ejovrh/misko/misko-prototype/functions.h

// forward declaration of this shitty function (it's at the very end of this file)
void poor_mans_debugging(void);

/* auto_timeout() - returns 1 if enough time has passed
 *  returns:
 *    1 if time is up
 *    0 otherwise
 *
 * input arguments:
 *    uint32_t some_button_press_time - time of button press
 *    uint8_t timeout - timeout in seconds
 *
 * times are in seconds !!
 */
uint8_t inline auto_timeout(const uint32_t in_button_press_time, const uint8_t timeout_val)
{
  return (abs( in_button_press_time - millis()) / 1000 > timeout_val ?  1 :  0);
}

// reads a byte from the ADXL345
byte adxl345_readByte(const byte registerAddress) // reads one byte at registerAddress
{
		digitalWrite(SPI_SS_ADXL345_pin, LOW); // reserve the slave
   	SPI.transfer(0x80 | registerAddress); // set the MSB to 1 (the read command), then send address to read from
		byte retval = SPI.transfer(0x00); // send one byte (0x00) into the circular FIFO buffer, get one byte back
		digitalWrite(SPI_SS_ADXL345_pin, HIGH); // release the slave
    return retval;  // return value
}

// writes a byte into the ADXL345
bool adxl345_writeByte(const byte registerAddress, const byte value)
{
	digitalWrite(SPI_SS_ADXL345_pin, LOW); // signal the slave
	SPI.transfer(registerAddress); // send address to write to
	SPI.transfer(value); // send the byte
	digitalWrite(SPI_SS_ADXL345_pin, HIGH); // release the slave

	if (adxl345_readByte(registerAddress) != value) // verify correct setting
	{
		Serial.print(F("registerAddress was not set:"));Serial.print(registerAddress);Serial.print("-");Serial.println(value);
		return 1;
	}

	return 0;
}

// writes one byte data into the FeRAM at address addr
uint8_t FeRAMWriteByte(const uint16_t addr, const byte data)
{
	if (addr > 0x7FFF) // if we try to go past the max. RAM address
		return 1;	// return something

	uint8_t addr_msb = (addr >> 8) & 0xFF;
	uint8_t addr_lsb = addr & 0xFF;

	// put the FeRAM module into RW mode
	digitalWrite(SPI_FRAM_SS_pin, LOW); // select the FeRAM module
	SPI.transfer(CMD_WREN);	// issue WREN command
	digitalWrite(SPI_FRAM_SS_pin, HIGH); // de-select the FeRAM module

	// put into write mode, send address, then write data
	digitalWrite(SPI_FRAM_SS_pin, LOW); // select the FeRAM module
	SPI.transfer(CMD_WRITE);	// issue WRITE command
	SPI.transfer(addr_msb); // send address most significant byte
	SPI.transfer(addr_lsb); // send address least significant byte

	SPI.transfer(data); // write data into module

	digitalWrite(SPI_FRAM_SS_pin, HIGH); // de-select the FeRAM module

	return 0;
}

// returns one one byte from the FeRAM at addr
byte FeRAMReadByte(const uint16_t addr)
{
	byte retval;
	if (addr > 0x7FFF) // if we try to go past the max. RAM address
		return -1;	// return something

	uint8_t addr_msb = (addr >> 8) & 0xFF;
	uint8_t addr_lsb = addr & 0xFF;

	digitalWrite(SPI_FRAM_SS_pin, LOW); // select the FeRAM module
	SPI.transfer(CMD_READ); // send READ command
	SPI.transfer(addr_msb);	// send address most significant byte
	SPI.transfer(addr_lsb); // send address least significant byte

	retval = SPI.transfer(0xFF); // send on byte of crap into the circular buffer, get one byte back

	digitalWrite(SPI_FRAM_SS_pin, HIGH); // de-select the FeRAM module

	return retval; // returns read out data
}

// writes string data of len lenght into FeRAM at address addr
uint8_t FeRAMWriteStr(const uint16_t addr, const char *data, uint8_t len)
{
	if (addr > 0x7FFF) // if we try to go past the max. RAM address
		return 1;	// return something

	uint8_t addr_msb = (addr >> 8) & 0xFF;
	uint8_t addr_lsb = addr & 0xFF;

	// put the FeRAM module into RW mode
	digitalWrite(SPI_FRAM_SS_pin, LOW); // select the FeRAM module
	SPI.transfer(CMD_WREN);	// issue WREN command
	digitalWrite(SPI_FRAM_SS_pin, HIGH); // de-select the FeRAM module

	// put into write mode, send address, then write data
	digitalWrite(SPI_FRAM_SS_pin, LOW); // select the FeRAM module
	SPI.transfer(CMD_WRITE);	// issue WRITE command
	SPI.transfer(addr_msb); // send address most significant byte
	SPI.transfer(addr_lsb); // send address least significant byte

	for (uint8_t i = 0; i< len; i++)
		SPI.transfer( *(data+i) ); // write data into module

	digitalWrite(SPI_FRAM_SS_pin, HIGH); // de-select the FeRAM module

	return 0;
}

// reads a string in FeRAM at addess addr of lenght len into buff
uint8_t FeRAMReadString(const uint16_t addr, char *out_data, uint8_t len)
{
	if (addr > 0x7FFF) // if we try to go past the max. RAM address
		return -1;	// return something

	memset(out_data, '\0', len);

	uint8_t addr_msb = (addr >> 8) & 0xFF;
	uint8_t addr_lsb = addr & 0xFF;

	digitalWrite(SPI_FRAM_SS_pin, LOW); // select the FeRAM module
	SPI.transfer(CMD_READ); // send READ command
	SPI.transfer(addr_msb);	// send address most significant byte
	SPI.transfer(addr_lsb); // send address least significant byte

	for(uint8_t i = 0; i < len; i++)
	{
		*(out_data+i) = SPI.transfer(0xFF); // send on byte of crap into the circular buffer, get one byte back
	}

	digitalWrite(SPI_FRAM_SS_pin, HIGH); // de-select the FeRAM module
}

 // returns the external voltage reference in volts
inline float read_Varef() // the external reference voltage is set to 2.50V via a zener diode
{
	return AREF_VOLTAGE;
}

// returns the voltage on a given pin
float calculate_voltage(int pin) // calculates the voltage on a given pin by considering read_aref_V()
{
	uint16_t reading = analogRead(pin); // read raw sensor data (voltage) - 10bit resolution -> values form 0-1023
	return (float) (reading * read_Varef() / 1024.0); // converting reading to voltage, based on AREF;
}

// calculates the temperature by reading voltage from the TMP36
inline float calculate_temperature(void) // executed from loop()
{
	return (calculate_voltage(TMP36_Vsense_pin) - 0.5) * 100.0 ;  // 10 mv per C, 500 mV offset
}

// callback for Vcc
const char *fn_cb_get_Vcc(m2_rom_void_p element)
{
	static char retval[9]; // will return something like Vcc3.23V
	static char tmp_vcc[5]; // holds e.g "3.23" as an intermediate conversion to string

	dtostrf(val_Vcc, 3, 2, tmp_vcc); // convert the float into a string
	sprintf(retval, "Vcc%sV", tmp_vcc ); // print the string into the retval string
	return retval;
}

// callback for battery percentage
const char *fn_cb_get_bat_pct(m2_rom_void_p element)
{
	// FIXME

	const char retval[9];
	sprintf("batA %3d%", val_batA_pct);
	return retval;

	//return "foo";
	//dtostrf(val_batA_pct, 3, 0, bat_a_pct + 4*sizeof(char)); // instead, this works
		//// http://www.atmel.com/webdoc/AVRLibcReferenceManual/group__avr__stdlib_1ga060c998e77fb5fc0d3168b3ce8771d42.html
	//strcat(bat_a_pct, "% ");
	//return bat_a_pct;
}

// handler for the bluetooth power toggle button
void handle_bluetooth_button(void)
{
	/* purpose: control BT power based on feram settings

		the button functions are, if auto mode is enabled:
			- press and the device turns on. after EERPOM_BLUETOOTH_AUTO_TIMEOUT_INDEX is over, turn off
			- hold pressed to keep the device on until manually turned off by again holding pressed (timeout then doesnt count)

		if auto mode is not enabled, the button does nothing.

		in order to accomplish this, we need to track in what mode we are in (EERPOM_BLUETOOTH_POWER_INDEX),
			how long the device is supposed to be turned on (EERPOM_BLUETOOTH_AUTO_TIMEOUT_INDEX) and how long the BT button
			was held pressed (bluetooth_button_press_time and bluetooth_button_release_time).

		additionally, we need to make sure that one button press equals one event - we need to know if the button is
			held pressed or not (flag_bluetooth_power_toggle_pressed)

	*/

	if (!flag_bluetooth_power_toggle_pressed) // if the button is not flagged as pressed
	{
		if(digitalRead(menu_gprs_power_button_pin) == HIGH) // if the button gets pressed
		{
			flag_bluetooth_power_toggle_pressed = 1; // flag the button as pressed, prevents multiple calls

	if ( ( (FeRAMReadByte(FERAM_DEVICE_MISC_CFG2) >> FERAM_DEVICE_MISC_CFG2_BLUETOOTH_POWER) & 0x03 ) != 2 )
				return; // do nothing

			if (flag_bluetooth_power_keep_on) // prevent the timer from starting when we want to turn off manually toggled power
				return; // do nothing

			bluetooth_button_press_time = millis(); // record time of button press; this is used in a bit down to keep bt on on auto
			digitalWrite(Bluetooth_wakeup_pin, LOW); // turn on the device
			flag_bluetooth_is_on = 1; // set flag to on
		}
	}
	else // the button is already flagged as pressed == is held pressed
	{
	if ( ( (FeRAMReadByte(FERAM_DEVICE_MISC_CFG2) >> FERAM_DEVICE_MISC_CFG2_BLUETOOTH_POWER) & 0x03 ) != 2 )
			return;

		if ( digitalRead(menu_gprs_power_button_pin) == LOW) // the button is released
		{
			bluetooth_button_release_time = millis(); // record time of button release
			flag_bluetooth_power_toggle_pressed = 0; // mark button as released

			if (abs(bluetooth_button_release_time - bluetooth_button_press_time) > 500) // if button is held long enough
						flag_bluetooth_power_keep_on = !flag_bluetooth_power_keep_on; // toggle the power state on -> off and vice versa
		}
	}

	if ( ( (FeRAMReadByte(FERAM_DEVICE_MISC_CFG2) >> FERAM_DEVICE_MISC_CFG2_BLUETOOTH_POWER) & 0x03 ) != 2 )
		return; // do nothing

	if (flag_bluetooth_power_keep_on) // if the BT device is marked to be kept on
		return;	// do nothing

	if ( flag_bluetooth_is_on && auto_timeout(bluetooth_button_press_time, FeRAMReadByte(FERAM_BLUETOOTH_AUTO_TIMEOUT)) ) // if the device is on and enough time has passed
	{
			digitalWrite(Bluetooth_wakeup_pin, HIGH); // turn off the device
			flag_bluetooth_is_on = 0; // set flag to off
			// flag_bluetooth_power_keep_on = 0;
	}
}

// handler for the bluetooth power toggle button
void handle_gprs_button(void)
{
	/*	purpose: control the GPRS module based on FeRAM settings
	 *
	 *	this function is called from loop and checks if a button press occured
	 *		if it did, it acts upon it
	 *
	 *	prerequisites for any GPRS action:
	 *		1. power on the GSM module & dialup
	 *		2. authenticate on HTTP server
	 *		3. do the task at hand
	 *		4. report status
	 *		5. tear down the connection & power off the GSM module
	 */

	if (!flag_gprs_push_pressed) // if the button is not flagged as pressed
	{
		if(digitalRead(menu_gprs_power_button_pin) == HIGH) // if the button gets pressed
		{
			uint8_t config = ( ( FeRAMReadByte(FERAM_DEVICE_MISC_CFG2) >> FERAM_DEVICE_MISC_CFG2_GPRS_FUNCTION) & 0x03 ); // fish out the device setting in FeRAM
			flag_gprs_push_pressed = 1; // flag the button as pressed, prevents multiple calls

			if (!config) // if it is set to do nothing...
				return; // then do nothing

			if (config == 1) // immediate push of position
			{
				Serial.println("immediate push of position");
			}

			if (config == 2) // upload all of today's logs
			{
				Serial.println("upload of today's logs");
			}

			if (config == 3) // FIXME: GPS fucking
			{
				poor_mans_debugging();
			}
		}
	}
	else // the button is already flagged as pressed
	{
		if ( digitalRead(menu_gprs_power_button_pin) == LOW) // the button is released
			flag_gprs_push_pressed = 0; // mark button as released
	}
}

// puts the oled to sleep accrding to config setting
void handle_lcd_sleep(void)
{
	if (flag_oled_sleep || ( (FeRAMReadByte(FERAM_DEVICE_MISC_CFG1) >> FERAM_DEVICE_MISC_CFG1_OLED_AUTO_POWER) & 0x01 ) ) // dont do anything on "on" setting or in sleep mode
		return;

	if (auto_timeout(lcd_button_press_time, FeRAMReadByte(FERAM_OLED_AUTO_TIMEOUT) )) // true if time is up
	{
		flag_oled_sleep = 1;
		OLED.sleepOn();
	}
}

// calculates NMEA checksum
uint8_t getCheckSum(char *string)
{
  int XOR = 0;

  // for (int i = 1; i < 20; i++)
  for (uint8_t i = 1; i < strlen(string) -1; i++)
    XOR = XOR ^ *(string+i);

  return XOR;
}

// NMEA checksum calculator
int16_t parseHex(char g)
{
  if (g >= '0' && g <= '9')
    return (g - '0');
  else
    if (g >= 'A' && g <= 'F')
      return (g + 10 - 'A');
    else
      if (g >= 'a' && g <= 'f')
        return (g + 10 - 'a');

  return (-1);
}

// sets the RMC/GGA sentence frequency by sending the EM406A module an appropriate NMEA config sentence
void gps_adjust_log_freq(void) // operates directly off values stored in FeRAM
{
	/* valid for MTK3333 and similar chipsets
	*	314_PMTK_API_SET_NMEA_OUTPUT is what configures it
	*	fields:
	*			0 NMEA_SEN_GLL, GPGLL interval - Geographic Position - Latitude longitude
	*->		1 NMEA_SEN_RMC, GNRMC interval - Recommended Minimum Specific GNSS Sentence
	*			2 NMEA_SEN_VTG, GPVTG interval - Course Over Ground and Ground Speed
	*->		3 NMEA_SEN_GGA, GPGGA interval - GPS Fix Data
	*->		4 NMEA_SEN_GSA, GPGSA interval - GNSS DOPS and Active Satellites
	*->		5 NMEA_SEN_GSV, GPGSV interval - GNSS Satellites in View
	*			6 NMEA_SEN_GRS, GPGRS interval - GNSS Range Residuals
	*			7 NMEA_SEN_GST, GPGST interval - GNSS Pseudorange Errors Statistics
	*
	*			13 NMEA_SEN_MALM, PMTKALM interval - GPS almanac information
	*			14 NMEA_SEN_MEPH, PMTKEPH interval - GPS ephmeris information
	*			15 NMEA_SEN_MDGP, PMTKDGP interval - GPS differential correction information
	*			16 NMEA_SEN_MDBG, PMTKDBG interval  MTK debug information
	*			17 NMEA_SEN_ZDA, GPZDA interval - Time & Date
	*			18 NMEA_SEN_MCHN, PMTKCHN interval - GNSS channel status
	*			19 NMEA_SEN_DTM, GPDTM interval - Datum reference
	*
	*		NMEA checksum calculator:
	*			http://www.hhhh.org/wiml/proj/nmeaxor.html
	*
	*/

	sprintf(gps_command_buffer, "$PMTK314,0,%d,0,%d,%d,%d,0,0,0,0,0,0,0,0,0,0,0,0,0,0*", // construct the command string
		(uint8_t) ( (FeRAMReadByte(FERAM_GPS_GPRMC_GGA_GSA_FREQ) >> FERAM_GPS_GPRMC_GGA_FREQ) & 0x0F ), // RMC - index 1
		(uint8_t) ( (FeRAMReadByte(FERAM_GPS_GPRMC_GGA_GSA_FREQ) >> FERAM_GPS_GPRMC_GGA_FREQ) & 0x0F ), // GGA - index 3
		(uint8_t) ( (FeRAMReadByte(FERAM_GPS_GPRMC_GGA_GSA_FREQ) >> FERAM_GPS_GPGSA_FREQ) & 0x0F ), // GGA - index 4
		(uint8_t) ( (FeRAMReadByte(FERAM_GPS_GPZDA_GSV_FREQ) >> FERAM_GPS_GPGSV_FREQ) & 0x0F )); // GSV - field 5

	sprintf(gps_command_buffer + strlen(gps_command_buffer), "%02X", getCheckSum(gps_command_buffer)); // append the checksum
	Serial.println(gps_command_buffer);
	gps.println(gps_command_buffer);
	return;
}

// callback for data datetime_ok button
void fn_cb_button_datetime_ok(m2_el_fnarg_p fnarg)
{
	m2_SetRootExtended(&top_el_expandable_menu, 1, 0);
}

// callback for data position_ok button
void fn_cb_button_position_ok(m2_el_fnarg_p fnarg)
{
	m2_SetRootExtended(&top_el_expandable_menu, 2, 0);
}

// callback for data cellular_ok button
void fn_cb_button_cellular_ok(m2_el_fnarg_p fnarg)
{
	m2_SetRootExtended(&top_el_expandable_menu, 3, 0);
}

// callback for data-device_status_ok button
void fn_cb_button_device_status_ok(m2_el_fnarg_p fnarg)
{
	m2_SetRootExtended(&top_el_expandable_menu, 4, 0);
}

// callback for settings logging_ok button
void fn_cb_button_logging_ok(m2_el_fnarg_p fnarg)
{
	m2_SetRootExtended(&top_el_expandable_menu, 2, 0);
}

// callback for settings serial_ok button
void fn_cb_button_serial_ok(m2_el_fnarg_p fnarg)
{
	m2_SetRootExtended(&top_el_expandable_menu, 3, 0);
}

// callback for settings timezone_ok button
void fn_cb_button_timezone_ok(m2_el_fnarg_p fnarg)
{
	m2_SetRootExtended(&top_el_expandable_menu, 4, 0);
}

// callback for settings bluetooth_ok button
void fn_cb_button_bluetooth_ok(m2_el_fnarg_p fnarg)
{
	m2_SetRootExtended(&top_el_expandable_menu, 5, 0);
}

// callback for settings display_ok button
void fn_cb_button_display_ok(m2_el_fnarg_p fnarg)
{
	m2_SetRootExtended(&top_el_expandable_menu, 6, 0);
}

// callback for settings gps_ok button
void fn_cb_button_gps_ok(m2_el_fnarg_p fnarg)
{
	m2_SetRootExtended(&top_el_expandable_menu, 7, 0);
}

// callback for settings gsm_ok button
void fn_cb_button_gsm_ok(m2_el_fnarg_p fnarg)
{
	m2_SetRootExtended(&top_el_expandable_menu, 8, 0);
}

// callback for settings accelerometer_ok button
void fn_cb_button_accelerometer_ok(m2_el_fnarg_p fnarg)
{
	m2_SetRootExtended(&top_el_expandable_menu, 9, 0);
}

// callback for UTC display
const char *fn_cb_get_utc(m2_rom_void_p element)
{
	static char retval[4] = ""; // e.g. -12 or  +3
	int8_t tz = (int8_t) FeRAMReadByte(FERAM_DEVICE_TIMEZONE); // fetch the setting from FeRAM

	if (tz < 0 )
		itoa(tz, retval, 10); // will have the "-" automatically
	else
	{
		retval[0] = '+';	// manually set the "+" sign
		retval[1] = '\0'; // terminate
		itoa(tz, retval+sizeof(char), 10);
	}
	return retval;
}

// callback for GSM device power status
const char *fn_cb_get_gsm_power_status(m2_rom_void_p element)
{
	if (flag_gsm_on)
		return "on";

	return "off";
;}

// callback for GSM device network status
const char *fn_cb_get_gsm_network_status(m2_rom_void_p element)
{
	if (!flag_gsm_on) // if the device is off
		return "n/a";

	return "netw";
}

// callback for GSM device upload status
// TODO - implement it
const char *fn_cb_get_gsm_upload_status(m2_rom_void_p element)
{
	if (!flag_gsm_on) // if the device is off
	return "n/a";

	return "foo1";
}

// callback for GSM device power status
const char *fn_cb_get_gsm_foo1(m2_rom_void_p element)
{
	if (!flag_gsm_on) // if the device is off
		return "n/a";

	return "foo1";
}

// callback for GSM device power status
const char *fn_cb_get_gsm_foo2(m2_rom_void_p element)
{
	if (!flag_gsm_on) // if the device is off
		return "n/a";

	return "foo2";
}

// callback for GSM device power status
const char *fn_cb_get_gsm_foo3(m2_rom_void_p element)
{
	if (!flag_gsm_on) // if the device is off
		return "n/a";

	return "foo3";
}

// callback for temperature
const char *fn_cb_get_temperature(m2_rom_void_p element)
{
	static char retval[6]; // holds retval of e.g. "T+24C" of "T-10C"
	sprintf(retval, "T%+02dC", (int8_t) round(val_temperature) ); // round & print the temperature as an integer into the retval string
	return retval;
}

// callback for bluetooth power setting
const char *fn_cb_set_bluetooth_power_setting(m2_rom_void_p element, uint8_t msg, uint8_t *valptr)
{
	uint8_t val;
	// see https://github.com/olikraus/m2tklib/wiki/elref#combofn
	switch(msg) // msg can be one of: M2_COMBOFN_MSG_GET_VALUE, M2_COMBOFN_MSG_SET_VALUE, M2_COMBOFN_MSG_GET_STRING
  {
		case M2_COMBOFN_MSG_GET_VALUE: // we get the vaue from feram
			*valptr = (FeRAMReadByte(FERAM_DEVICE_MISC_CFG2) >> FERAM_DEVICE_MISC_CFG2_BLUETOOTH_POWER) & 0x03; // see if bit 1 is set
      break;

    case M2_COMBOFN_MSG_SET_VALUE: // we set the value into feram
			val = FeRAMReadByte(FERAM_DEVICE_MISC_CFG2); // retrieve byte
			// TODO: these two lines can probably be written more beautiful
			val &= ~ (1 << FERAM_DEVICE_MISC_CFG2_BLUETOOTH_POWER); // hopefully set these two bits to 0 (so that they dont poison the subsequent write)
			val &= ~ (1 << (FERAM_DEVICE_MISC_CFG2_BLUETOOTH_POWER +1) );
			FeRAMWriteByte( FERAM_DEVICE_MISC_CFG2, val ^ (*valptr << FERAM_DEVICE_MISC_CFG2_BLUETOOTH_POWER) );	// now save the new bit values & write the crap
      break;

    case M2_COMBOFN_MSG_GET_STRING: // we get the string _and_ set it (implicitly via M2_COMBOFN_MSG_SET_VALUE) via *valptr
      if (*valptr == 0) // values are coded in fram.h
			{
				digitalWrite(Bluetooth_wakeup_pin, HIGH);
        return "off";
			}

      if (*valptr == 1)
			{
				digitalWrite(Bluetooth_wakeup_pin, LOW);
        return "on";
			}

      if (*valptr == 2)
			{
				digitalWrite(Bluetooth_wakeup_pin, HIGH);
        return "auto";
			}
  }

  return NULL;
}

// callback for bluetooth power setting
const char *fn_cb_set_gsm_function(m2_rom_void_p element, uint8_t msg, uint8_t *valptr)
{
	uint8_t val;
	// see https://github.com/olikraus/m2tklib/wiki/elref#combofn
	switch(msg) // msg can be one of: M2_COMBOFN_MSG_GET_VALUE, M2_COMBOFN_MSG_SET_VALUE, M2_COMBOFN_MSG_GET_STRING
	{
		case M2_COMBOFN_MSG_GET_VALUE: // we get the vaue from feram
		*valptr = (FeRAMReadByte(FERAM_DEVICE_MISC_CFG2) >> FERAM_DEVICE_MISC_CFG2_GPRS_FUNCTION) & 0x03; // see if bit 1 is set
		break;

		case M2_COMBOFN_MSG_SET_VALUE: // we set the value into feram
		val = FeRAMReadByte(FERAM_DEVICE_MISC_CFG2); // retrieve byte
		// TODO: these two lines can probably be written more beautiful
		val &= ~ (1 << FERAM_DEVICE_MISC_CFG2_GPRS_FUNCTION); // hopefully set these two bits to 0 (so that they dont poison the subsequent write)
		val &= ~ (1 << (FERAM_DEVICE_MISC_CFG2_GPRS_FUNCTION +1) );
		FeRAMWriteByte( FERAM_DEVICE_MISC_CFG2, val ^ (*valptr << FERAM_DEVICE_MISC_CFG2_GPRS_FUNCTION) );	// now save the new bit values & write the crap
		break;

		case M2_COMBOFN_MSG_GET_STRING: // we get the string _and_ set it (implicitly via M2_COMBOFN_MSG_SET_VALUE) via *valptr
		if (*valptr == 0) // values are coded in fram.h
			return "off";

		if (*valptr == 1)
			return "imm. upload";

		if (*valptr == 2)
			return "EOD upload";

		if (*valptr == 3)
			return "GPS dbg";

	}

	return NULL;
}

// callback for OLED power setting
const char *fn_cb_set_oled_power_setting(m2_rom_void_p element, uint8_t msg, uint8_t *valptr)
{
	// see fn_cb_set_bluetooth_power_setting for comments
	switch(msg)
  {
		case M2_COMBOFN_MSG_GET_VALUE:
			*valptr = (FeRAMReadByte(FERAM_DEVICE_MISC_CFG1) >> FERAM_DEVICE_MISC_CFG1_OLED_AUTO_POWER) & 0x01; // see if bit 1 is set
			break;

    case M2_COMBOFN_MSG_SET_VALUE:
			FeRAMWriteByte(FERAM_DEVICE_MISC_CFG1, FeRAMReadByte(FERAM_DEVICE_MISC_CFG1) ^ (1<<FERAM_DEVICE_MISC_CFG1_OLED_AUTO_POWER)); // set it 1
			break;

    case M2_COMBOFN_MSG_GET_STRING:
      if (*valptr == 0)
        return "auto";

      if (*valptr == 1)
        return "on";
  }

  return NULL;
}

// callback for GPS power setting
const char *fn_cb_set_gps_power_setting(m2_rom_void_p element, uint8_t msg, uint8_t *valptr)
{
	// see fn_cb_set_bluetooth_power_setting for comments
	switch(msg)
  {
		case M2_COMBOFN_MSG_GET_VALUE:
			*valptr = (FeRAMReadByte(FERAM_GPS_MISC_CFG) >> FERAM_GPS_MISC_CFG_POWER_CTL) & 0x01;
      break;

    case M2_COMBOFN_MSG_SET_VALUE:
			FeRAMWriteByte(FERAM_GPS_MISC_CFG, FeRAMReadByte(FERAM_GPS_MISC_CFG) ^ (1<<FERAM_GPS_MISC_CFG_POWER_CTL)); // set it 1
			break;

    case M2_COMBOFN_MSG_GET_STRING:
      if (*valptr == 0)
        return "off";
		//if (*valptr == 1)
		else
        return "on";
  }

  return NULL;
}

// callback for NMEA sentence printout setting
const char *fn_cb_nmea_printout_setting(m2_rom_void_p element, uint8_t msg, uint8_t *valptr)
{
	// see fn_cb_set_bluetooth_power_setting for comments
	switch(msg)
	{
		case M2_COMBOFN_MSG_GET_VALUE:
		*valptr = (FeRAMReadByte(FERAM_GPS_MISC_CFG) >> FERAM_GPS_MISC_CFG_NMEA_PRINT_TO_SERIAL) & 0x01;
		break;

		case M2_COMBOFN_MSG_SET_VALUE:
		FeRAMWriteByte(FERAM_GPS_MISC_CFG, FeRAMReadByte(FERAM_GPS_MISC_CFG) ^ (1<<FERAM_GPS_MISC_CFG_NMEA_PRINT_TO_SERIAL)); // set it 1
		break;

		case M2_COMBOFN_MSG_GET_STRING:
		if (*valptr == 0)
			return "off";
		//if (*valptr == 1)
		else
			return "on";
	}

	return NULL;
}

// callback for serial port setting
const char *fn_cb_set_serial_setting(m2_rom_void_p element, uint8_t msg, uint8_t *valptr)
{
	// see fn_cb_set_bluetooth_power_setting for comments
	switch(msg)
  {
		uint8_t val;
		case M2_COMBOFN_MSG_GET_VALUE:
			*valptr = (FeRAMReadByte(FERAM_DEVICE_MISC_CFG2) >> FERAM_DEVICE_MISC_CFG2_SYSTEM_SERIAL) & 0x03; // see if bit 1 is set
			break;

    case M2_COMBOFN_MSG_SET_VALUE:
			val = FeRAMReadByte(FERAM_DEVICE_MISC_CFG2); // retrieve byte
			// TODO: these two lines can probably be written more beautiful
			val &= ~ (1 << FERAM_DEVICE_MISC_CFG2_SYSTEM_SERIAL); // hopefully set these two bits to 0 (so that they dont poison the subsequent write)
			val &= ~ (1 << (FERAM_DEVICE_MISC_CFG2_SYSTEM_SERIAL +1) );
			FeRAMWriteByte( FERAM_DEVICE_MISC_CFG2, val ^ (*valptr << FERAM_DEVICE_MISC_CFG2_SYSTEM_SERIAL) );	// now save the new bit values & write the crap
			break;

    case M2_COMBOFN_MSG_GET_STRING:
      if (*valptr == 0)
        return "GPS";

      if (*valptr == 1)
        return "GSM";

			if (*valptr == 2)
        return "system";

	}

  return NULL;
}

// callback for GSM power setting
// TODO: test me
const char *fn_cb_set_gsm_power(m2_rom_void_p element, uint8_t msg, uint8_t *valptr)
{
	// see fn_cb_set_bluetooth_power_setting for comments
	switch(msg)
  {
		case M2_COMBOFN_MSG_GET_VALUE:
		*valptr = (FeRAMReadByte(FERAM_GSM_MISC_CFG) >> FERAM_GSM_MISC_CFG_POWER_CTL) & 0x01;
		break;

		case M2_COMBOFN_MSG_SET_VALUE:
		FeRAMWriteByte(FERAM_GSM_MISC_CFG, FeRAMReadByte(FERAM_GSM_MISC_CFG) ^ (1<<FERAM_GSM_MISC_CFG_POWER_CTL)); // set it 1
		break;

    case M2_COMBOFN_MSG_GET_STRING:
      if (*valptr == 0)
			{
        return "off";
			}

      if (*valptr == 1)
			{
        return "on";
			}
  }

  return NULL;
}

// callback for GSM APN setting
// TODO: test me
const char *fn_cb_gsm_apn(m2_rom_void_p element, uint8_t msg, uint8_t *valptr)
{
	// see fn_cb_set_bluetooth_power_setting for comments
	switch(msg)
	{
		case M2_COMBOFN_MSG_GET_VALUE:
		*valptr = (FeRAMReadByte(FERAM_GSM_MISC_CFG) >> FERAM_GSM_MISC_CFG_POWER_CTL) & 0x01;
		break;

		case M2_COMBOFN_MSG_SET_VALUE:
		FeRAMWriteByte(FERAM_GSM_MISC_CFG, FeRAMReadByte(FERAM_GSM_MISC_CFG) ^ (1<<FERAM_GSM_MISC_CFG_POWER_CTL)); // set it 1
		break;

		case M2_COMBOFN_MSG_GET_STRING:
		if (*valptr == 0)
		{
			return "off";
		}

		if (*valptr == 1)
		{
			return "on";
		}
	}

	return NULL;
}

// callback for GSM http server setting
// TODO: test me
const char *fn_cb_gsm_http_server(m2_rom_void_p element, uint8_t msg, uint8_t *valptr)
{
	// see fn_cb_set_bluetooth_power_setting for comments
	switch(msg)
	{
		case M2_COMBOFN_MSG_GET_VALUE:
		*valptr = (FeRAMReadByte(FERAM_GSM_MISC_CFG) >> FERAM_GSM_MISC_CFG_POWER_CTL) & 0x01;
		break;

		case M2_COMBOFN_MSG_SET_VALUE:
		FeRAMWriteByte(FERAM_GSM_MISC_CFG, FeRAMReadByte(FERAM_GSM_MISC_CFG) ^ (1<<FERAM_GSM_MISC_CFG_POWER_CTL)); // set it 1
		break;

		case M2_COMBOFN_MSG_GET_STRING:
		if (*valptr == 0)
		{
			return "off";
		}

		if (*valptr == 1)
		{
			return "on";
		}
	}

	return NULL;
}

// callback for GSM power setting
// TODO: test me
const char *fn_cb_gsm_credentials(m2_rom_void_p element, uint8_t msg, uint8_t *valptr)
{
	// see fn_cb_set_bluetooth_power_setting for comments
	switch(msg)
	{
		case M2_COMBOFN_MSG_GET_VALUE:
		*valptr = (FeRAMReadByte(FERAM_GSM_MISC_CFG) >> FERAM_GSM_MISC_CFG_POWER_CTL) & 0x01;
		break;

		case M2_COMBOFN_MSG_SET_VALUE:
		FeRAMWriteByte(FERAM_GSM_MISC_CFG, FeRAMReadByte(FERAM_GSM_MISC_CFG) ^ (1<<FERAM_GSM_MISC_CFG_POWER_CTL)); // set it 1
		break;

		case M2_COMBOFN_MSG_GET_STRING:
		if (*valptr == 0)
		{
			return "off";
		}

		if (*valptr == 1)
		{
			return "on";
		}
	}

	return NULL;
}

// callback for SD write setting
const char *fn_cb_set_sd_write(m2_rom_void_p element, uint8_t msg, uint8_t *valptr)
{
	// see fn_cb_set_bluetooth_power_setting for comments
	switch(msg)
  {
		case M2_COMBOFN_MSG_GET_VALUE:
			*valptr = (FeRAMReadByte(FERAM_DEVICE_MISC_CFG1) >> FERAM_DEVICE_MISC_CFG1_SD_WRITE) & 0x01;
			break;

    case M2_COMBOFN_MSG_SET_VALUE:
			FeRAMWriteByte(FERAM_DEVICE_MISC_CFG1, FeRAMReadByte(FERAM_DEVICE_MISC_CFG1) ^  (1<<FERAM_DEVICE_MISC_CFG1_SD_WRITE) ); // set it 1
			break;

    case M2_COMBOFN_MSG_GET_STRING:
      if (*valptr == 0)
        return "off";
		if (*valptr == 1)
        return "on";
  }

  return NULL;
}

// callback for statistics write setting
const char *fn_cb_set_stat_write(m2_rom_void_p element, uint8_t msg, uint8_t *valptr)
{
	// see fn_cb_set_bluetooth_power_setting for comments
	switch(msg)
	{
		case M2_COMBOFN_MSG_GET_VALUE:
		*valptr = (FeRAMReadByte(FERAM_DEVICE_MISC_CFG1) >> FERAM_DEVICE_MISC_CFG1_STAT_WRITE) & 0x01;
		break;

		case M2_COMBOFN_MSG_SET_VALUE:
		FeRAMWriteByte(FERAM_DEVICE_MISC_CFG1, FeRAMReadByte(FERAM_DEVICE_MISC_CFG1) ^  (1<<FERAM_DEVICE_MISC_CFG1_STAT_WRITE) ); // set it 1
		break;

		case M2_COMBOFN_MSG_GET_STRING:
		if (*valptr == 0)
		return "off";
		if (*valptr == 1)
		return "on";
	}

	return NULL;
}

// callback for timezone setting
int8_t fn_cb_set_tz(m2_rom_void_p element, uint8_t msg, int8_t val)
{
  if ( msg == M2_U8_MSG_GET_VALUE ) // if we get a GET message
    return (uint8_t) FeRAMReadByte(FERAM_DEVICE_TIMEZONE);

  if ( msg == M2_U8_MSG_SET_VALUE ) // if we get a SET message
		FeRAMWriteByte(FERAM_DEVICE_TIMEZONE, val);

	return FeRAMReadByte(FERAM_DEVICE_TIMEZONE);
}

// callback for ADXL345 activity power setting
const char *fn_cb_set_accel_enable(m2_rom_void_p element, uint8_t msg, uint8_t *valptr)
{
	// see fn_cb_set_bluetooth_power_setting for comments
	switch(msg)
	{
		case M2_COMBOFN_MSG_GET_VALUE:
			*valptr = ( FeRAMReadByte(FERAM_DEVICE_MISC_CFG1) >> FERAM_DEVICE_MISC_CFG1_ADXL345_AUTO_POWER ) & 0x01;
			break;

		case M2_COMBOFN_MSG_SET_VALUE:
			FeRAMWriteByte(FERAM_DEVICE_MISC_CFG1, FeRAMReadByte(FERAM_DEVICE_MISC_CFG1) ^ (1<<FERAM_DEVICE_MISC_CFG1_ADXL345_AUTO_POWER));
			break;

		case M2_COMBOFN_MSG_GET_STRING:
		if (*valptr == 0)
		{
			adxl345_writeByte(INT_ENABLE, INT_DISABLE_CFG);
			return "off";
		}
		else
		{
			adxl345_writeByte(INT_ENABLE, INT_ENABLE_CFG);
			return "on";
		}
	}

	return NULL;
}

// callback for accelerometer timeout value setting
int8_t fn_cb_set_accel_timeout(m2_rom_void_p element, uint8_t msg, int8_t val)
{
	if ( msg == M2_U8_MSG_GET_VALUE ) // if we get a GET message
	return (uint8_t) FeRAMReadByte(FERAM_ADXL345_MOVEMENT_TIMEOUT);

	if ( msg == M2_U8_MSG_SET_VALUE ) // if we get a SET message
	{
	 FeRAMWriteByte(FERAM_ADXL345_MOVEMENT_TIMEOUT, val);
	 adxl345_writeByte(TIME_INACT, val);
	}
	return FeRAMReadByte(FERAM_ADXL345_MOVEMENT_TIMEOUT);
}

// callback for accelerometer inativity threshold setting
int8_t fn_cb_set_inact_threshold(m2_rom_void_p element, uint8_t msg, int8_t val)
{
	if ( msg == M2_U8_MSG_GET_VALUE ) // if we get a GET message
	return (uint8_t) FeRAMReadByte(FERAM_ADXL345_INACTIVITY_THRESHOLD);

	if ( msg == M2_U8_MSG_SET_VALUE ) // if we get a SET message
	{
		FeRAMWriteByte(FERAM_ADXL345_INACTIVITY_THRESHOLD, val);
		adxl345_writeByte(TIME_INACT, val);
	}
	return FeRAMReadByte(FERAM_ADXL345_INACTIVITY_THRESHOLD);
}

// callback for accelerometer ativity threshold setting
int8_t fn_cb_set_act_threshold(m2_rom_void_p element, uint8_t msg, int8_t val)
{
	if ( msg == M2_U8_MSG_GET_VALUE ) // if we get a GET message
	return (uint8_t) FeRAMReadByte(FERAM_ADXL345_ACTIVITY_THRESHOLD);

	if ( msg == M2_U8_MSG_SET_VALUE ) // if we get a SET message
	{
		FeRAMWriteByte(FERAM_ADXL345_ACTIVITY_THRESHOLD, val);
		adxl345_writeByte(TIME_INACT, val);
	}
	return FeRAMReadByte(FERAM_ADXL345_ACTIVITY_THRESHOLD);
}

// callback for bluetooth timeout
uint8_t fn_cb_set_bluetooth_timeout(m2_rom_void_p element, uint8_t msg, uint8_t val)
{
  if ( msg == M2_U8_MSG_GET_VALUE ) // if we get a GET message
    return (uint8_t) FeRAMReadByte(FERAM_BLUETOOTH_AUTO_TIMEOUT); // get value

  if ( msg == M2_U8_MSG_SET_VALUE ) // if we get a SET message
		FeRAMWriteByte(FERAM_BLUETOOTH_AUTO_TIMEOUT, val);

	return (uint8_t) FeRAMReadByte(FERAM_BLUETOOTH_AUTO_TIMEOUT);
}

// callback for OLED timeout
uint8_t fn_cb_set_oled_timeout(m2_rom_void_p element, uint8_t msg, uint8_t val)
{
  if ( msg == M2_U8_MSG_GET_VALUE ) // if we get a GET message
		return (uint8_t) FeRAMReadByte(FERAM_OLED_AUTO_TIMEOUT); // get val

  if ( msg == M2_U8_MSG_SET_VALUE ) // if we get a SET message
		FeRAMWriteByte(FERAM_OLED_AUTO_TIMEOUT, val); // set val

	return (uint8_t) FeRAMReadByte(FERAM_OLED_AUTO_TIMEOUT); // ...so that we dont have an non-return for this type of function
}

// callback for gps GPRMC and GPGGA log frequency
uint8_t fn_cb_set_gps_rmc_gga_log_freq(m2_rom_void_p element, uint8_t msg, uint8_t val)
{
  if ( msg == M2_U8_MSG_GET_VALUE ) // if we get a GET message
    return (uint8_t) ( (FeRAMReadByte(FERAM_GPS_GPRMC_GGA_GSA_FREQ) >> FERAM_GPS_GPRMC_GGA_FREQ) & 0x0F ); // convert the rightmost 4 bits to a number

  if ( msg == M2_U8_MSG_SET_VALUE ) // if we get a SET message
	{ // populate bit fields in FeRAM
		uint8_t outval = FeRAMReadByte(FERAM_GPS_GPRMC_GGA_GSA_FREQ); // retrieve byte
		// TODO: these two lines can probably be written more beautiful
		outval &= ~ (1 << (FERAM_GPS_GPRMC_GGA_FREQ +0) ); // hopefully set these 4 bits to 0 (so that they dont poison the subsequent write)
		outval &= ~ (1 << (FERAM_GPS_GPRMC_GGA_FREQ +1) );
		outval &= ~ (1 << (FERAM_GPS_GPRMC_GGA_FREQ +2) );
		outval &= ~ (1 << (FERAM_GPS_GPRMC_GGA_FREQ +3) );
		FeRAMWriteByte( FERAM_GPS_GPRMC_GGA_GSA_FREQ, outval ^ (val << FERAM_GPS_GPRMC_GGA_FREQ) );	// now save the new bit values & write the crap

		gps_adjust_log_freq(); // call function, which in turn sends the actual command to the gps device
	}
}

// callback for gps GPGSV log frequency
uint8_t fn_cb_set_gps_gsv_log_freq(m2_rom_void_p element, uint8_t msg, uint8_t val)
{
	if ( msg == M2_U8_MSG_GET_VALUE ) // if we get a GET message
	return (uint8_t) ( (FeRAMReadByte(FERAM_GPS_GPZDA_GSV_FREQ) >> FERAM_GPS_GPGSV_FREQ) & 0x0F ); // convert the rightmost 4 bits to a number

	if ( msg == M2_U8_MSG_SET_VALUE ) // if we get a SET message
	{ // populate bit fields in FeRAM
		uint8_t outval = FeRAMReadByte(FERAM_GPS_GPZDA_GSV_FREQ); // retrieve byte
		// TODO: these two lines can probably be written more beautiful
		outval &= ~ (1 << (FERAM_GPS_GPGSV_FREQ +0) ); // hopefully set these 4 bits to 0 (so that they dont poison the subsequent write)
		outval &= ~ (1 << (FERAM_GPS_GPGSV_FREQ +1) );
		outval &= ~ (1 << (FERAM_GPS_GPGSV_FREQ +2) );
		outval &= ~ (1 << (FERAM_GPS_GPGSV_FREQ +3) );
		FeRAMWriteByte( FERAM_GPS_GPZDA_GSV_FREQ, outval ^ (val << FERAM_GPS_GPGSV_FREQ) );	// now save the new bit values & write the crap

		gps_adjust_log_freq(); // call function, which in turn sends the actual command to the gps device
	}
}

// callback for gps GPGSA log frequency
uint8_t fn_cb_set_gps_gsa_log_freq(m2_rom_void_p element, uint8_t msg, uint8_t val)
{
  if ( msg == M2_U8_MSG_GET_VALUE ) // if we get a GET message
  return (uint8_t) ( (FeRAMReadByte(FERAM_GPS_GPRMC_GGA_GSA_FREQ) >> FERAM_GPS_GPGSA_FREQ) & 0x0F ); // convert the rightmost 4 bits to a number

  if ( msg == M2_U8_MSG_SET_VALUE ) // if we get a SET message
  { // populate bit fields in FeRAM
	  uint8_t outval = FeRAMReadByte(FERAM_GPS_GPRMC_GGA_GSA_FREQ); // retrieve byte
	  // TODO: these two lines can probably be written more beautiful
	  outval &= ~ (1 << (FERAM_GPS_GPGSA_FREQ +0) ); // hopefully set these 4 bits to 0 (so that they dont poison the subsequent write)
	  outval &= ~ (1 << (FERAM_GPS_GPGSA_FREQ +1) );
	  outval &= ~ (1 << (FERAM_GPS_GPGSA_FREQ +2) );
	  outval &= ~ (1 << (FERAM_GPS_GPGSA_FREQ +3) );
	  FeRAMWriteByte( FERAM_GPS_GPRMC_GGA_GSA_FREQ, outval ^ (val << FERAM_GPS_GPGSA_FREQ) );	// now save the new bit values & write the crap

		gps_adjust_log_freq(); // call function, which in turn sends the actual command to the gps device
	}
}

// callback for gps GPZDA log frequency
uint8_t fn_cb_set_gps_zda_log_freq(m2_rom_void_p element, uint8_t msg, uint8_t val)
{
	if ( msg == M2_U8_MSG_GET_VALUE ) // if we get a GET message
{
	//FIXME: without the print's the display gets garbled
	Serial.print("foo:");
	Serial.print((uint8_t) ( (FeRAMReadByte(FERAM_GPS_GPZDA_GSV_FREQ) >> FERAM_GPS_GPZDA_FREQ) & 0x0F ));
	Serial.println(":foo");  // convert the rightmost 4 bits to a number
  return (uint8_t) ( (FeRAMReadByte(FERAM_GPS_GPZDA_GSV_FREQ) >> FERAM_GPS_GPZDA_FREQ) & 0x0F );
}

	if ( msg == M2_U8_MSG_SET_VALUE ) // if we get a SET message
	{ // populate bit fields in FeRAM
		uint8_t outval = FeRAMReadByte(FERAM_GPS_GPZDA_GSV_FREQ); // retrieve byte
		// TODO: these two lines can probably be written more beautiful
		outval &= ~ (1 << (FERAM_GPS_GPZDA_FREQ +0) ); // hopefully set these 4 bits to 0 (so that they dont poison the subsequent write)
		outval &= ~ (1 << (FERAM_GPS_GPZDA_FREQ +1) );
		outval &= ~ (1 << (FERAM_GPS_GPZDA_FREQ +2) );
		outval &= ~ (1 << (FERAM_GPS_GPZDA_FREQ +3) );
		FeRAMWriteByte( FERAM_GPS_GPZDA_GSV_FREQ, outval ^ (val << FERAM_GPS_GPZDA_FREQ) );	// now save the new bit values & write the crap

		gps_adjust_log_freq(); // call function, which in turn sends the actual command to the gps device
	}
}

// callback for MCP73871 battery charge status
// TODO: needs to be tested with a battery
const char *fn_cb_get_bat_charge_status(m2_rom_void_p element)
{
	if (digitalRead(MCP73871_power_good_pin) == LOW) // see MCP83871 datasheet p.21
	{
		if (digitalRead(MCP73871_charge_status_1_pin) == HIGH || digitalRead(MCP73871_charge_status_2_pin) == LOW)
			return "charged";
		if (digitalRead(MCP73871_charge_status_1_pin) == LOW || digitalRead(MCP73871_charge_status_2_pin) == HIGH)
			return "charging";
		if (digitalRead(MCP73871_charge_status_1_pin) == HIGH || digitalRead(MCP73871_charge_status_2_pin) == HIGH)
			return "STANDBY";
	}

	if (digitalRead(MCP73871_power_good_pin) == HIGH)
	{
		if (digitalRead(MCP73871_charge_status_1_pin) == LOW || digitalRead(MCP73871_charge_status_2_pin) == HIGH)
			return "BATT LOW";
		if (digitalRead(MCP73871_charge_status_1_pin) == HIGH || digitalRead(MCP73871_charge_status_2_pin) == HIGH)
			return "SHUTD";
	}

	return "foo";
}

// callback for MCP73871 input power status
const char *fn_cb_get_power_good_status(m2_rom_void_p element)
{
	if (digitalRead(MCP73871_power_good_pin) == LOW)
		return "ExtPw ok ";

		return "ExtPw off ";
}

// callback for gps latitude
const char *fn_cb_get_gps_latitude(m2_rom_void_p element)
{
		return gps_latitude;
}

// callback for gps longtitude
const char *fn_cb_get_gps_longtitude(m2_rom_void_p element)
{
		return gps_longtitude;
}

// callback for gps altitude
const char *fn_cb_get_gps_altitude(m2_rom_void_p element)
{
	static char retval[10]; // will return e.g. "-333m" or "+5555m"
	uint8_t len = strlen(gps_altitude);

	if (len == 0) // if no altitude is given
		sprintf(retval, "alt -m"); // print "alt" and a dummy into retval
	else
		sprintf(retval, "alt %sm", gps_altitude); // print "alt" and the actual number-string into retval

	return retval;
}

// callback for gps satellites in view
const char *fn_cb_get_gps_satellites_in_view(m2_rom_void_p element)
{
	static char retval[7]; // will return something like "0.00" or "99.99"
	uint8_t len = strlen(gps_satellites_in_view); // lenght of HDOP string

	if (len == 0) // empty string (only a null terminator)
		sprintf(retval, "sat --"); // copy "sat" and the actual number-string into retval
	else
		sprintf(retval, "sat %s", gps_satellites_in_view); // copy "sat" and the actual number-string into retval

	return retval; // return that val
}

// callback for the position fix indicator
const char *fn_cb_get_gps_fix_indicator(m2_rom_void_p element)
{
		if (!flag_gps_on && digitalRead(GPS_power_ctl_pin == LOW))
			return "dev. off";

		switch(gps_position_fix_indicator)
		{
			case '1':
				return "SPS";

			case '2':
				return "DGPS";

			case '3':
				return "PPS";

			case '4':
				return "RTK";

			case '5':
				return "FRTK";

			case '6':
				return "est.";

			case '7':
				return "man.";

			case '8':
				return "sim.";

			case '0':
			default:
				return "inv.";
		}

}

// callback for gps HDOP
const char *fn_cb_get_gps_hdop(m2_rom_void_p element)
{
	static char retval[10];
	uint8_t len = strlen(gps_hdop);

	if (len == 0) // empty string or not?
		sprintf(retval, "hdop --.--"); // copy "hdop" and the actual number-string into retval
	else
		sprintf(retval, "hdop %s", gps_hdop); // copy "hdop" and the actual number-string into retval

	return retval; // return that val
}

// send contents of file over serial to host PC
void print_to_serial(const char *in_string)
{
	Serial.println(in_string);
	 File dataFile = SD.open(in_string);

  if (dataFile)
	{
		Serial.println(F("START ---"));
		Serial.print(in_string);Serial.print(F(" size "));Serial.print(dataFile.size()/1024);Serial.println(F("kB"));

    while (dataFile.available())
		{
      Serial.write(dataFile.read());
    }

    dataFile.close();
		Serial.println();
		Serial.print(in_string);Serial.println(F(" END ---"));
		Serial.println();
}
}

//M2tk function for FAT directory content retrieval
const char *fs_strlist_getstr(uint8_t idx, uint8_t msg)
{
  if (msg == M2_STRLIST_MSG_GET_STR)
	{
    /* Check for the extra button: Return string for this extra button */
    if ( idx == 0 )
      return "..";

		/* Not the extra button: Return file/directory name */

    mas_GetDirEntry(idx - 1);
    return mas_GetFilename();
  }

	if ( msg == M2_STRLIST_MSG_GET_EXTENDED_STR )
	{
		/* Check for the extra button: Return icon for this extra button */
		if ( idx == 0 )
			return "a";       /* arrow left of the m2icon font */

		/* Not the extra button: Return file or directory icon */
		mas_GetDirEntry(idx - 1);

		if ( mas_IsDir() )
			return "A";       /* folder icon of the m2icon font */
		return "B";         /* file icon of the m2icon font */
	}

	if ( msg == M2_STRLIST_MSG_SELECT ) // button right
	{
		/* Check for the extra button: Execute button action */
		if ( idx == 0 )
		{
				if ( mas_GetPath()[0] == '\0' )
					m2_SetRoot(&top_el_expandable_menu);
				else
				{
					mas_ChDirUp();
					m2_SetRoot(m2_GetRoot());  /* reset menu to first element, send NEW_DIALOG and force recount */
				}
					/* Not the extra button: Goto subdir or return (with selected file) */
		}
		else
		{
				mas_GetDirEntry(idx - 1);
				if ( mas_IsDir() )
				{
					mas_ChDir(mas_GetFilename());
					m2_SetRoot(m2_GetRoot());  /* reset menu to first element, send NEW_DIALOG and force recount */
				}
				else
				{
						print_to_serial(mas_GetFilename()); // send the filename to print_to_serial() for TX over serial to e.g. putty
				}
			}
	}

	if ( msg == M2_STRLIST_MSG_NEW_DIALOG )
	{Serial.println(mas_GetDirEntryCnt());
		/* (re-) calculate number of entries, limit no of entries to 250 */
		if ( mas_GetDirEntryCnt() < 250-1 )
			fs_m2tk_cnt = mas_GetDirEntryCnt()+1;
		else
			fs_m2tk_cnt = 250;
	}

	return NULL;
}

// buffered write onto SD card utilizing a circular buffer
void sd_buffer_write(char *dst_buffer, char *in_string, uint8_t in_size, File filehandle)
{
	/* this function writes in_string of in_size into dst_buffer and eventually via filehandle
	 *	onto the SD card.
	 *	the intent is to buffer NMEA sentences / device statistics and write in bulk (as opposed to
	 *		every e.g. second) and thus save the SD card from being burned to death by too frequent
	 *		write operations.
	 */

	// pointer arithmetrics, beware!
	static char *end = dst_buffer + SD_BUFFERSIZE; // end address of buffer
	static char *target = dst_buffer; // at init time is start address of sd_buffer, otherwise is current of next free write dst. addr
	static bool flag_flush_1st = 0; // flag 1st half of buffer for flushing
	static bool flag_flush_2nd = 0; // flag 2nd half of buffer for flushing

	#if BUFFER_DEBUG_PRINT
		Serial.print("buffer start:");Serial.println((uint16_t)dst_buffer);
		Serial.print("buffer end:");Serial.println((uint16_t) end);
		Serial.print("target:");Serial.println((uint16_t) target - (uint16_t)dst_buffer );
		Serial.print("space left:");Serial.println((uint16_t) end - (uint16_t)target );
		Serial.print("in_size");Serial.println(in_size);
	#endif

	/* we need to cyclically write into the buffer and make sure we dont write past the buffer end address:
			if we have a sring that would go past buffer end address, we truncate it, fill up the buffer until
			the end addr with as much string that fits and then write the rest of the string at the beginning of
			the buffer.

		every time we do this, we need to check if the 1st half (or the 2nd half) of the buffer are filled
			with fresh data; if so, we need to flush it onto the SD card.

		*in_string points to the global variable NMEA_buffer, in_size bytes in lenght.
			per NMEA standard, the NMEA sentence can be maximally 82 characters long (80 + \r\n)
	*/
	if (target < end - (in_size * sizeof(char)) ) // if one NMEA sentence will fit
	// simply write into the buffer
	{
		#if BUFFER_DEBUG_PRINT
			Serial.println("if");
		#endif

		target = (char *) memcpy(target, in_string, in_size); // copy onto location of c and return position of destination
		target += in_size*sizeof(char); // advance target by ammount of bytes copied to the next free space

		if (!flag_flush_1st && target >= dst_buffer + (SD_BUFFERSIZE/2)*sizeof(char)) // if we have filled 1st half of the buffer
			flag_flush_1st = 1; // mark the 1st buffer for flushing

		if (!flag_flush_2nd && target < dst_buffer + (SD_BUFFERSIZE/2)*sizeof(char)) // if we have filled 1st half of the buffer
			flag_flush_2nd = 1; // mark the 2nd buffer for flushing

	}
	else // the incoming sentence will not fully fit
	// write what fits until the end of sd_buffer and the rest from beginning of sd_buffer
	{
		#if BUFFER_DEBUG_PRINT
			Serial.println("else");
		#endif

		uint16_t len = (uint16_t)end - (uint16_t)target; // how much free space is left? [difference in addresses]
		uint16_t rest = (uint16_t)in_size - len; // how much will not fit? [difference in number of bytes]

		#if BUFFER_DEBUG_PRINT
			Serial.print("len:");Serial.println(len);
			Serial.print("rest:");Serial.println(rest );
		#endif

		// first, flush the 1st half of the buffer
		if (flag_flush_1st)
		{
			digitalWrite(gps_red_led_pin, LOW); // turn on led to make write cycle start visible

			#if BUFFER_DEBUG_PRINT
				Serial.println("flushing 1st half");
			#else
				filehandle.write(dst_buffer, (SD_BUFFERSIZE/2)*sizeof(char)); // write 1st half of the buffer
				filehandle.flush(); // flush all to card
			#endif

			flag_flush_1st = 0; // unmark it
		}

		memcpy(target, in_string, len); // write that much into buffer
		target = dst_buffer; // set pointer back to start

		target = (char *) memcpy(target, in_string+len*sizeof(char), rest*sizeof(char)); // write the rest
		target += rest*sizeof(char); // advance target by ammount of bytes copied to the next free space

		// now we can flush the 2nd half of the buffer
		if (flag_flush_2nd)
		{
			#if BUFFER_DEBUG_PRINT
				Serial.println("flushing 2nd half");
			#else
				filehandle.write(dst_buffer+(SD_BUFFERSIZE/2)*sizeof(char), (SD_BUFFERSIZE/2)*sizeof(char)); // write 2nd half of the buffer
				filehandle.flush(); // flush all to card
			#endif

			flag_flush_2nd = 0; // unmark it
			digitalWrite(gps_red_led_pin, HIGH); // turn off led to make write cycle end visible
		}
	}
}

// determines baud rate (approximately)
uint32_t detectBaud(int pin)
{
	uint16_t rate = 10000;
	uint16_t x;

	for (uint8_t i = 0; i < 10; i++)
	{
		x = pulseIn(pin,LOW);   // measure the next zero bit width
    rate = x < rate ? x : rate;
	}

	if (rate < 12)
		return 115200;

  if (rate < 20)
		return 57600;

	if (rate < 29)
		return 38400;

	if (rate < 40)
		return 28800;

	if (rate < 60)
		return 19200;

	if (rate < 80)
		return 14400;

	if (rate < 150)
		return 9600;

	if (rate < 300)
		return 4800;

	if (rate < 600)
		return 2400;

	if (rate < 1200)
		return 1200;

  return 0;
 }

 // determines fix or not, parses coordinates, time
void gps_parse_gprmc(char *in_str)
{
	/*
	 * sample NMEA GPRMC sentence
	 *		$GNRMC,214329.000,A,4547.9089,N,01555.1553,E,1.33,121.79,121116,,,A*7A
   *    $GPRMC,221939.869,V,,,,,,,060816,,,N*41
   *    $GNRMC,214325.073,V,,,,,1.48,112.99,121116,,,N*5F
   *
	 *
	 * fields of interest (0-indexed), irrelevant are marked with an !:
	 *
	 *	 #0 - talker ID
	 *	 #1 - UTC time
	 *	 #2 - fix indicator: A - valid, V - invalid
	 *	 #3 - latitude; "4547.9089" in above example
	 *	 #4 - latitude indicator; "N" in above example
	 *	 #5 - longtitude; "01555.1553" in above example
	 *	 #6 - longtitude indicator; "E" in above exmaple
	 *	 #7 - speed over ground in knots; "1.33" in above example
	 *!	 #8 - course, ; "121.79" in above example
	 *	 #9 - date in DDMMYY format; "121116" in above example
	 *!	 #10 - magnetic variation
	 *!	 #11 - magnetic variation indicator
	 */

	uint8_t i = 0; // counter for the string tokenizer

	char *p = strtok(in_str, ","); // char pointer for strtok

	while (p != NULL) // for as long as there is something to tokenize with the given delimiter...
	{
		if (i == 1)	// field 1 - hhmmss time data: 170942.000,A,4547.9094,N,01555.1254,E,0.13,142.38,050816,,,A*63
			memcpy(gps_time, p, 6* sizeof(char)); // fill char gps_time[7] = "XXXXXX" by copying from one array into another

		if (i == 2)	// field 2 - fix indicator: A,4547.9094,N,01555.1254,E,0.13,142.38,050816,,,A*63
			flag_gps_fix = ( *p == 'A' ? 1 : 0 ); // sets flag_gps_fix to 1 if there is a fix

		if (i == 3)	// field 3 - latitude: 4547.9094,N,01555.1254,E,0.13,142.38,050816,,,A*63
		  if (flag_gps_fix)
			  memcpy(gps_latitude+(4*sizeof(char)), p, 9 * sizeof(char)); // fill up gps_latitude[] , part 1

		if (i == 4) // field 4 - latitude indicator: N,01555.1254,E,0.13,142.38,050816,,,A*63
		  if (flag_gps_fix)
			  memcpy(gps_latitude+(13*sizeof(char)), p, sizeof(char)); // fill up gps_latitude[] , part 2

		if (i == 5)	// field 5 - longtitude: 01555.1254,E,0.13,142.38,050816,,,A*63
			if (flag_gps_fix)
				memcpy(gps_longtitude+(4*sizeof(char)), p, 10 * sizeof(char)); // fill up gps_longtitude[] , part 1

		if (i == 6) // field 6 - longtitude indicator: E,0.13,142.38,050816,,,A*63
			if (flag_gps_fix)
				memcpy(gps_longtitude+(14*sizeof(char)), p, sizeof(char)); // fill up gps_longtitude[] , part 2, appends letter

		if (i == 7)	// field 7 - speed over ground: 0.13,142.38,050816,,,A*63
		  if (flag_gps_fix)
				// TODO: this needs to be verified under real world conditions (i.e. real movement with varying speeds)
				gps_speed = atoi(p);

		if (i == 9)	// field 9 - date: 050816,,,A*63
		{
			//Serial.print("p");Serial.println(p);
			//FIXME: needs a check if the reported time is recent (i.e. not literally the start of the GPS epoch - 1.6. 1980)
				// fill gps_date
				*(gps_date+2) = *(p+4);  // Y - 1
				*(gps_date+3) = *(p+5);  // Y - 6
				*(gps_date+4) = *(p+2);  // M - 0
				*(gps_date+5) = *(p+3);  // M - 8
				*(gps_date+6) = *(p+0);  // D - 0
				*(gps_date+7) = *(p+1);  // D - 5
				break;
		}

		p = strtok(NULL, ","); // set the tokenizer for the next iteration
		i++; // counter increment
	}
}

// parses out satellites used, HDOP, MSL altitude
void gps_parse_gpgga(char *in_str)
{
	/*
	 *	$GNGGA,214323.073,,,,,0,0,,,M,,M,,*57
	 *	$GNGGA,214326.073,4547.9072,N,01555.1584,E,1,5,1.59,140.9,M,42.5,M,,*43
	 *
	 *	fields of interest (0-indexed) are marked with an X:
	 *	#0 - talker ID
	 *	#1 - UTC time
	 *	#2 - latitude
	 *	#3 - north/south
	 *	#4 - longtitude
	 *	#5 - east/west
	 *X	#6 - position fix indicator: "1" after the "E," in the above example)
	 *			0 - invalid
	 *			1 - GPS (SPS)
	 *			2 - DGPS
	 *			3 - PPS
	 *			4 - real time kinetic
	 *			5 - float real time kinetic
	 *			6 - estimated
	 *			7 - manual input
	 *			8 - simulation mode
	 *X	#7 - satellites used: "5" in the above example
	 *X	#8 - HDOP: "1.59" in the above example
	 *X	#9 - MSL altitude: "140.9" in the above example
	 *	#10 - unit: "M"
	 *	#11 - height above geoid: "42.5" in the above example
	 *	#12 - unit: "M"
	 *
	 */

	uint8_t i = 0; // counter for the string tokenizer

	char *p = strtok(in_str, ","); // char pointer for strtok

	while (p != NULL) // for as long as there is something to tokenize with the given delimiter...
	{
		if (i == 6) // position fix indicator
			gps_position_fix_indicator = *p; // it's just one char (number)

		if (i == 7) // satellites used
		{
			memset(gps_satellites_in_view, '\0', 3); // set the whole container to \0
			memcpy( gps_satellites_in_view, p, strcspn (p, ",") * sizeof(char) ); // copy an adequate lenght of bytes from src into the container
		}

		if (i == 8) // hdop
		{
			memset(gps_hdop, '\0', 5);
			memcpy( gps_hdop, p, strcspn (p, ",") * sizeof(char) );
		}

		if (i == 9) // altitude
		{
			memset(gps_altitude, '\0', 5);
			memcpy( gps_altitude, p, strcspn (p, ".,") * sizeof(char) ); // copy the numbers...
		}

		p = strtok(NULL, ","); // set the tokenizer for the next iteration
		i++; // counter increment
	}
}

// constructs a PMTK741 positin hint message based on a last good known position
//TODO
char *pmtk741( )
{

	/*
	 * sample NMEA GPRMC sentence
	 *		$GNRMC,214329.000,A,4547.9089,N,01555.1553,E,1.33,121.79,121116,,,A*7A
	 *
	 * fields of interest (0-indexed), irrelevant are marked with an !:
	 *
	 *	 #0 - talker ID
	 *	 #1 - UTC time
	 *	 #2 - fix indicator: A - valid, V - invalid
	 *X	 #3 - latitude; "4547.9089" in above example
	 *	 #4 - latitude indicator; "N" in above example
	 *X	 #5 - longtitude; "01555.1553" in above example
	 *	 #6 - longtitude indicator; "E" in above exmaple
	 *	 #7 - speed over ground in knots; "1.33" in above example
	 *	 #8 - course, ; "121.79" in above example
	 *	 #9 - date in DDMMYY format; "121116" in above example
	 *	 #10 - magnetic variation
	 *	 #11 - magnetic variation indicator
	 *
	 *	 the PMTK741 sentence we are constructing looks like:
	 *	 $PMTK741,45.479094,015.551375,120,2016,12,02,17,40,00*1B
	 *
	 *	 fields are (0-indexed):
	 *	  0 - message type
	 *		1 - latitude
	 *		2 - longtitude
	 *		3 - altitude
	 *		4 - year
	 *		5 - month
	 *		6 - day
	 *		7 - hour
	 *		8 - minute
	 *		9 - seconds
	 *		10 - checksum
	 */

	char retval[61] = "";

//	sprintf("$PMTK741,%s,%s,%s,%.4s,%.2s,%.2s,%.2s,%.2s,%.2s*", gps_longtitude, gps_latitude, gps_altitude, gps_date, gps_date+3, gps_date+5, gps_time, gps_time+2, gps_time+4);

	return retval;
}

// primitive BT button-activated printout
void poor_mans_debugging(void)
{
	// poor man's debugging

		//Serial.print("temp:");Serial.print(temp);Serial.println(":");

	//Serial.print("FERAM_DEVICE_MISC_CFG2 ");
	//Serial.println(FeRAMReadByte(FERAM_DEVICE_MISC_CFG2), BIN);

	//Serial.print("bt:");Serial.print(FeRAMReadByte(FERAM_DEVICE_MISC_CFG2), BIN);Serial.println(":bt");
	//	Serial.print("FERAM_GPS_GPRMC_GGA_GSA_FREQ");Serial.println(FeRAMReadByte(FERAM_GPS_GPRMC_GGA_GSA_FREQ), BIN);
	//	Serial.print("FERAM_GPS_GPZDA_GSV_FREQ");Serial.println(FeRAMReadByte(FERAM_GPS_GPZDA_GSV_FREQ), BIN);

	//gps.println("$PMTK220,1000*1F");

	// issue a factory reset to the gps device
	//gps.println("$PMTK104*37");

	//current pos:$GNRMC,172715.000,A,4547.9094,N,01555.1375,E,0.00,326.01,031216,,,A*74
	//Serial.println("$PMTK741,45.479094,015.551375,120,2016,12,02,17,40,00*1B");

	char rmc[83] = "";
	char gga[83] = "";
	FeRAMReadString(FERAM_GPS_LAST_GOOD_GNRMC, rmc, 82);
	FeRAMReadString(FERAM_GPS_LAST_GOOD_GNGGA, gga, 82);

	if (!flag_gps_fix)
		gps_parse_gprmc(rmc);
	if (!flag_gps_fix)
		gps_parse_gpgga(gga);

	Serial.print("rmc:");Serial.print(rmc);Serial.println(":rmc");
	Serial.print("gga:");Serial.print(gga);Serial.println(":gga");


/* 		char buffer[82];
		sprintf(buffer, "$PSRF104,%s,%s,%s,75000,%s,%s,12,1", gps_latitude, gps_longtitude, gps_altitude, gps_time_of_week, gps_week);
		Serial.println(buffer);
		//Serial1.write("$PSRF109,124*34\r\n"); */

}
