ejovrh/misko/misko-prototype/display.h

/*
 * here the display is defined
 *
 * references for the libraries used are:
 * https://github.com/olikraus/u8glib/wiki
 * https://github.com/olikraus/m2tklib/wiki/ghref
 * https://github.com/olikraus/m2tklib/wiki
 */

// display construction start

M2_SPACE(el_whitespace, "W6h8");

// data start
	// datetime
		M2_BUTTON(el_datetime_ok, format_rf0, "ok", fn_cb_button_datetime_ok);
		M2_LABEL(el_gps_date, format_rf0, gps_date); // label for gps_date
		M2_LABEL(el_gps_time, format_rf0, gps_time); // label for gps_time
		M2_LIST(el_list_datetime) = {&el_gps_date, &el_whitespace, &el_gps_time};
		M2_HLIST(el_hlist_datetime, format_rf0, el_list_datetime);
		M2_LABEL(el_utc, format_rf0, "UTC");
		M2_LABELFN(el_gps_utc, format_rf0, fn_cb_get_utc); // timezone string
		M2_LIST(el_list_utc) = {&el_utc, &el_whitespace, &el_gps_utc};
		M2_HLIST(el_hlist_utc, format_rf0, el_list_utc);
		M2_LIST(el_datetime_list) { &el_hlist_datetime, &el_hlist_utc, &el_datetime_ok} ;
		M2_GRIDLIST(el_datetime_grid, "c1", el_datetime_list);
		M2_ALIGN(el_top_datetime_menu, format_1W64H64, &el_datetime_grid);
	// datetime

	// position
		M2_BUTTON(el_position_ok, format_rf0, "ok", &fn_cb_button_position_ok);
		M2_LABELFN(el_gps_latitude, format_rf0, fn_cb_get_gps_latitude);
		M2_LABELFN(el_gps_longtitude, format_rf0, fn_cb_get_gps_longtitude);
		M2_LABELFN(el_gps_altitude, format_rf0, fn_cb_get_gps_altitude);
		M2_LABELFN(el_gps_sat_in_view, format_rf0, fn_cb_get_gps_satellites_in_view);
		M2_LABELFN(el_gps_hdop, format_rf0, fn_cb_get_gps_hdop);
		M2_LABELFN(el_gps_position_fix, format_rf0, fn_cb_get_gps_fix_indicator);
		M2_LIST(el_gps_alt_fix_list) = {&el_gps_altitude, &el_whitespace, &el_gps_position_fix};
		M2_HLIST(el_gps_hlist_alt_fix_list, format_rf0, el_gps_alt_fix_list);
		M2_LIST(el_sat_dop_list) = {&el_gps_sat_in_view, &el_whitespace, &el_gps_hdop};
		M2_HLIST(el_hlist_sat_dop, format_rf0, el_sat_dop_list);
		M2_LIST(el_gps_list) = {&el_gps_latitude, &el_gps_longtitude, &el_gps_hlist_alt_fix_list, &el_hlist_sat_dop, &el_position_ok};
		M2_GRIDLIST(el_gps_grid, "c1", el_gps_list);
		M2_ALIGN(el_top_gps_menu, format_1W64H64, &el_gps_grid);
	// position

	// cellular
		M2_BUTTON(el_cellular_ok, format_rf0, "ok", &fn_cb_button_cellular_ok);
		M2_LABEL(el_gsm_power_str, format_rf0, "power");
		M2_LABELFN(el_gsm_power_status, format_rf0, fn_cb_get_gsm_power_status);
		M2_LIST(el_gsm_power_list) = {&el_gsm_power_str, &el_whitespace, &el_gsm_power_status};
		M2_HLIST(el_gsm_power_hlist, format_rf0, el_gsm_power_list);
		M2_LABEL(el_gsm_network_str, format_rf0, "network");
		M2_LABELFN(el_gsm_network_status, format_rf0, fn_cb_get_gsm_network_status);
		M2_LIST(el_gsm_network_list) = {&el_gsm_network_str, &el_whitespace, &el_gsm_network_status};
		M2_HLIST(el_gsm_network_hlist, format_rf0, el_gsm_network_list);
		M2_LABEL(el_gsm_foo1_str, format_rf0, "upload status");
		M2_LABELFN(el_gsm_foo1, format_rf0, fn_cb_get_gsm_upload_status);
		M2_LIST(el_gsm_foo1_list) = {&el_gsm_foo1_str, &el_whitespace, &el_gsm_foo1};
		M2_HLIST(el_gsm_foo1_hlist, format_rf0, el_gsm_foo1_list);
		M2_LABEL(el_gsm_foo2_str, format_rf0, "foo2");
		M2_LABELFN(el_gsm_foo2, format_rf0, fn_cb_get_gsm_foo2);
		M2_LIST(el_gsm_foo2_list) = {&el_gsm_foo2_str, &el_whitespace, &el_gsm_foo2};
		M2_HLIST(el_gsm_foo2_hlist, format_rf0, el_gsm_foo2_list);
		M2_LABEL(el_gsm_foo3_str, format_rf0, "foo3");
		M2_LABELFN(el_gsm_foo3, format_rf0, fn_cb_get_gsm_foo3);
		M2_LIST(el_gsm_foo3_list) = {&el_gsm_foo3_str, &el_whitespace, &el_gsm_foo3, &el_whitespace, &el_cellular_ok};
		M2_HLIST(el_gsm_foo3_hlist, format_rf0, el_gsm_foo3_list);
		M2_LIST(el_gsm_list) = {&el_gsm_power_hlist, &el_gsm_network_hlist, &el_gsm_foo1_hlist, &el_gsm_foo2_hlist, &el_gsm_foo3_hlist};
		M2_GRIDLIST(el_gsm_grid, "c1", el_gsm_list);
		M2_ALIGN(el_top_gsm_menu, format_1W64H64, &el_gsm_grid);
	// cellular

	// device status
		M2_BUTTON(el_device_status_ok, format_rf0, "ok", &fn_cb_button_device_status_ok);
		M2_LABELFN(el_power_good, "fr0", fn_cb_get_power_good_status);
		M2_LABELFN(el_batt_charge, format_rf0, fn_cb_get_bat_charge_status);
		M2_LIST(el_power_list) = {&el_power_good, &el_whitespace, &el_batt_charge};
		M2_HLIST(el_power_hlist, format_rf0, el_power_list);
		//M2_LABELFN(el_batt_a, format_rf0, fn_cb_get_bat_pct);
		M2_LABEL(el_batt_a, format_rf0, "batA000%"); // FIXME
		M2_LABEL(el_batt_b, format_rf0, "batB000%"); // TODO
		M2_LABELFN(el_vcc, format_rf0, fn_cb_get_Vcc);
		M2_LIST(el_list_batt) = {&el_batt_a, &el_whitespace, &el_batt_b};
		M2_HLIST(el_hlist_batt, format_rf0, el_list_batt);
		M2_LABELFN(el_temperature, format_rf0, fn_cb_get_temperature);
		M2_LIST(el_list_vcc_temp) = {&el_vcc, &el_whitespace, &el_temperature};
		M2_HLIST(el_hlist_vcc_temp, format_rf0, el_list_vcc_temp);
		M2_LIST(el_device_misc_list) = {&el_power_hlist, &el_hlist_batt, &el_hlist_vcc_temp, &el_device_status_ok};
		M2_GRIDLIST(el_device_misc_grid, "c1", el_device_misc_list);
		M2_ALIGN(el_top_device_misc_menu, format_1W64H64, &el_device_misc_grid);
	// device status

	// SD card
		M2_STRLIST(el_fs_strlist, "l5f0W55", &fs_m2tk_first, &fs_m2tk_cnt, fs_strlist_getstr);
		// M2_SPACE(el_fs_space, "W1h1");
		// M2_VSB(el_fs_strlist_vsb, "l5W4r1", &fs_m2tk_first, &fs_m2tk_cnt);
		M2_LIST(list_fs_strlist) = { &el_fs_strlist};
		// M2_HLIST(el_fs_hlist, format_rf0, list_fs_strlist);
		M2_GRIDLIST(el_fs_grid, "c2", list_fs_strlist);
		M2_ALIGN(el_top_sd_content_menu, "-1|1W64H64", &el_fs_grid);
	// SD card
// data end

// settings start
	// logging
		M2_BUTTON(el_logging_ok, format_rf0, "ok", &fn_cb_button_logging_ok);
		M2_LABEL(el_sd_write, format_rf0, "Log position");
		M2_COMBOFN(el_sd_write_setting, format_rf0, 2, fn_cb_set_sd_write);
		M2_LABEL(el_stat_write, format_rf0, "Log statistics");
		M2_COMBOFN(el_stat_write_setting, format_rf0, 2, fn_cb_set_stat_write);
		M2_LIST(el_sd_list) = { &el_sd_write, &el_sd_write_setting, &el_stat_write, &el_stat_write_setting, &el_logging_ok };
		M2_GRIDLIST(el_sd_grid, "c2", el_sd_list);
		M2_ALIGN(el_top_settings_sd_menu, "-1|1W64H64", &el_sd_grid);
	// logging

	// serial port
		M2_BUTTON(el_serial_ok, format_rf0, "ok", &fn_cb_button_serial_ok);
		M2_LABEL(el_serial, format_rf0, "serial port");
		M2_COMBOFN(el_serial_setting, format_rf0, 3, fn_cb_set_serial_setting);
		M2_LIST(el_serial_list) = { &el_serial, &el_serial_setting, &el_serial_ok };
		M2_GRIDLIST(el_serial_grid, "c2", el_serial_list);
		M2_ALIGN(el_top_settings_serial_menu, "-1|1W64H64", &el_serial_grid);
	// serial port

	// timezone
		M2_BUTTON(el_timezone_ok, format_rf0, "ok", &fn_cb_button_timezone_ok);
		M2_LABEL(el_timezone_utc, format_rf0, "UTC");
		M2_S8NUMFN(el_timezone_utc_value, "+1c2", -12, 12, fn_cb_set_tz);
		M2_LIST(el_timezone_list) = { &el_timezone_utc, &el_timezone_utc_value, &el_timezone_ok };
		M2_GRIDLIST(el_timezone_grid, "c2", el_timezone_list);
		M2_ALIGN(el_top_settings_timezone_menu, "-1|1W64H64", &el_timezone_grid);
	// timezone

	// Bluetooth
		M2_BUTTON(el_bluetooth_ok, format_rf0, "ok", &fn_cb_button_bluetooth_ok);
		M2_LABEL(el_bluetooth_power, format_rf0, "Power");
		M2_COMBOFN(el_bluetooth_power_value, format_rf0, 3, fn_cb_set_bluetooth_power_setting);
		M2_S8NUMFN(el_bluetooth_power_timeout, "+0c1f0", 1, 5, fn_cb_set_bluetooth_timeout);
		M2_LIST(el_bluetooth_list) = { &el_bluetooth_power, &el_bluetooth_power_value, &el_bluetooth_power_timeout, &el_bluetooth_ok };
		M2_GRIDLIST(el_bluetooth_grid, "c2", el_bluetooth_list);
		M2_ALIGN(el_top_settings_bluetooth_menu, "-1|1W64H64", &el_bluetooth_grid);
	// Bluetooth

	// display
		M2_BUTTON(el_display_ok, format_rf0, "ok", &fn_cb_button_display_ok);
		M2_LABEL(el_lcd_power, format_rf0, "Power");
		M2_COMBOFN(el_lcd_power_value, format_rf0, 2, fn_cb_set_oled_power_setting);
		M2_S8NUMFN(el_lcd_power_timeout, "+0c1f0", 1, 5, fn_cb_set_oled_timeout);
		M2_LIST(el_lcd_list) = { &el_lcd_power, &el_lcd_power_value, &el_lcd_power_timeout, &el_display_ok };
		M2_GRIDLIST(el_lcd_grid, "c2", el_lcd_list);
		M2_ALIGN(el_top_settings_oled_menu, "-1|1W64H64", &el_lcd_grid);
	// display

	// GPS
		M2_BUTTON(el_gps_ok, format_rf0, "ok", &fn_cb_button_gps_ok);
		M2_LABEL(el_gps_power, format_rf0, "Power");
		M2_COMBOFN(el_gps_power_value, "f0", 2, fn_cb_set_gps_power_setting);
		M2_LIST(el_gps_list_power) = {&el_gps_power, &el_whitespace, &el_gps_power_value};
		M2_HLIST(el_gps_hlist_power, "l5f0W64", el_gps_list_power);
		M2_LABEL(el_gps_nmea_printout, format_rf0, "NMEA printout");
		M2_COMBOFN(el_gps_nmea_printout_value, "f0", 2, fn_cb_nmea_printout_setting);
		M2_LIST(el_gps_list_nmea_printout) = {&el_gps_nmea_printout, &el_whitespace, &el_gps_nmea_printout_value};
		M2_HLIST(el_gps_hlist_nmea_printout, "l5f0W64", el_gps_list_nmea_printout);
		M2_LABEL(el_gps_rmc_gga_freq, format_rf0, "RMC/GGA");
		M2_S8NUMFN(el_gps_freq_value, "+0c2f0", 1, 15, fn_cb_set_gps_rmc_gga_log_freq);
		M2_LABEL(el_gps_gsa_freq, format_rf0, "GSA");
		M2_S8NUMFN(el_gps_gsa_freq_value, "+0c2f0", 0, 15, fn_cb_set_gps_gsa_log_freq);
		M2_LIST(el_gps_list_rmc_gga_gsa) = {&el_gps_rmc_gga_freq, &el_gps_freq_value, &el_whitespace, &el_gps_gsa_freq, &el_gps_gsa_freq_value};
		M2_HLIST(el_gps_hlist_rmc_gga, "l5f0W64", el_gps_list_rmc_gga_gsa);
		M2_LABEL(el_gps_gsv_freq, format_rf0, "GSV");
		M2_S8NUMFN(el_gps_gsv_freq_value, "+0c2f0", 0, 15, fn_cb_set_gps_gsv_log_freq);
		//M2_LABEL(el_gps_zda_freq, format_rf0, "ZDA");
		//M2_S8NUMFN(el_gps_zda_freq_value, "+0c2f0", 0, 5, fn_cb_set_gps_zda_log_freq);
		M2_LIST(el_gps_list_gsv) = {&el_gps_gsv_freq, &el_gps_gsv_freq_value};
		M2_HLIST(el_gps_hlist_gsv, "l5f0W64", el_gps_list_gsv);
		M2_LIST(el_gps_settings_list) = { &el_gps_hlist_power, &el_gps_hlist_nmea_printout, &el_gps_hlist_rmc_gga, &el_gps_hlist_gsv, &el_gps_ok };
		M2_VLIST(el_gps_settings_vlist, NULL, el_gps_settings_list);
		//M2_GRIDLIST(el_gps_settings_grid, "c2", el_gps_settings_vlist);
		M2_ALIGN(el_top_settings_gps_menu, format_1W64H64, &el_gps_settings_vlist);
	// GPS end

	// GSM start
		M2_BUTTON(el_gsm_ok, format_rf0, "ok", &fn_cb_button_gsm_ok);
		M2_LABEL(el_gsm_settings_power_str, format_rf0, "GSM Power: ");
		M2_COMBOFN(el_gsm_power_val, format_rf0, 2, fn_cb_set_gsm_power);
		// TODO: check!
		M2_LABEL(el_gsm_settings_function_str, format_rf0, "btn. func.");
		M2_COMBOFN(el_gsm_settings_function_val, "f0", 4, fn_cb_set_gsm_function);
		M2_LABEL(el_gsm_settings_apn_str, format_rf0, "APN: ");
		M2_TEXT(el_gsm_settings_apn_val, "a0f0", gsm_apn, 63);
		//M2_LABEL(el_gsm_settings_http_server_str, format_rf0, "HTTP server: ");
		//M2_TEXT(el_gsm_settings_http_server_val, "a1f0", gsm_http_server, 63);
		//M2_LABEL(el_gsm_settings_cred_val, format_rf0, "cred.: ");
		//M2_TEXT(el_gsm_settings_cred_str, "f0", gsm_http_cred, 10);
		//M2_LIST(el_gsm_settings_list) = { &el_gsm_settings_power_str, &el_gsm_power_val, &el_gsm_settings_apn_str, &el_gsm_settings_apn_val, &el_gsm_settings_http_server_str, &el_gsm_settings_http_server_val, &el_gsm_settings_cred_val, &el_gsm_settings_cred_str, &el_gsm_ok };
		M2_LIST(el_gsm_settings_list) = { &el_gsm_settings_power_str, &el_gsm_power_val, &el_gsm_settings_function_str, &el_gsm_settings_function_val, &el_gsm_settings_apn_str, &el_gsm_settings_apn_val, &el_gsm_ok };
		M2_GRIDLIST(el_gsm_settings_grid, "c2", el_gsm_settings_list);
		M2_ALIGN(el_top_settings_gsm_menu, "-1|1W64H64", &el_gsm_settings_grid);
	// GSM end

	// accelerometer
	M2_BUTTON(el_accelerometer_ok, format_rf0, "ok", &fn_cb_button_accelerometer_ok);
	M2_LABEL(el_accel_str, format_rf0, "Trigger Sleep:");
	M2_COMBOFN(el_accel_enable_value, format_rf0, 2, fn_cb_set_accel_enable);
	M2_LABEL(el_accel_sleep_str, format_rf0, "Motion Timeout:");
	M2_S8NUMFN(el_accel_timeout, "+0c2f0", 1, 15, fn_cb_set_accel_timeout);
	M2_LABEL(el_accel_act_thresh_str, format_rf0, "Inact. Treshold:");
	M2_S8NUMFN(el_accel_act_thresh_val, "+0c2f0", 1, 15, fn_cb_set_act_threshold);
	M2_LABEL(el_accel_inact_thresh_str, format_rf0, "Act. Treshold:");
	M2_S8NUMFN(el_accel_inact_thresh_val, "+0c2f0", 1, 15, fn_cb_set_inact_threshold);
	M2_LIST(el_accel_list) = { &el_accel_str, &el_accel_enable_value, &el_accel_sleep_str, &el_accel_timeout, &el_accel_act_thresh_str, &el_accel_act_thresh_val, &el_accel_inact_thresh_str, &el_accel_inact_thresh_val, &el_accelerometer_ok };
	M2_GRIDLIST(el_accel_grid, "c2", el_accel_list);
	M2_ALIGN(el_top_settings_accel_menu, "-1|1W64H64", &el_accel_grid);
	// accelerometer
// settings end

m2_menu_entry m2_2lmenu_data[] =
{
  { "Data", NULL },
  { ". Datetime", &el_top_datetime_menu },
  { ". Position", &el_top_gps_menu },
	{ ". Cellular", &el_top_gsm_menu },
  { ". Device Status", &el_top_device_misc_menu},
	{ ". SD card", &el_top_sd_content_menu},
  { "Settings", NULL },
	{ ". Logging", &el_top_settings_sd_menu},
	{ ". Serial port", &el_top_settings_serial_menu},
  { ". Timezone", &el_top_settings_timezone_menu },
  { ". Bluetooth", &el_top_settings_bluetooth_menu },
  { ". Display", &el_top_settings_oled_menu },
  { ". GPS", &el_top_settings_gps_menu },
	{ ". GSM", &el_top_settings_gsm_menu },
	{ ". accelerometer", &el_top_settings_accel_menu },
  { NULL, NULL },
};

uint8_t m2_2lmenu_first; // first visible line
uint8_t m2_2lmenu_cnt; // total visible lines

M2_2LMENU(el_2lmenu, "l5f0e0W55", &m2_2lmenu_first, &m2_2lmenu_cnt, m2_2lmenu_data, ' ', ' ', '\0');
M2_SPACE(el_space, "W1h1");
M2_VSB(el_vsb, "l5w4r1", &m2_2lmenu_first, &m2_2lmenu_cnt);
M2_LIST(list_2lmenu) = { &el_2lmenu, &el_space, &el_vsb };
M2_HLIST(el_hlist, NULL, list_2lmenu);
M2_ALIGN(top_el_expandable_menu, "-1|1W64H64", &el_hlist);

M2tk m2(&top_el_expandable_menu, m2_es_arduino, m2_eh_4bs, m2_gh_u8g_ffs); // m2 object and constructor

// display construction end
